bjc01/Drone_Drama_v2/D&Dv2 etch/8038 value 150dpi.png

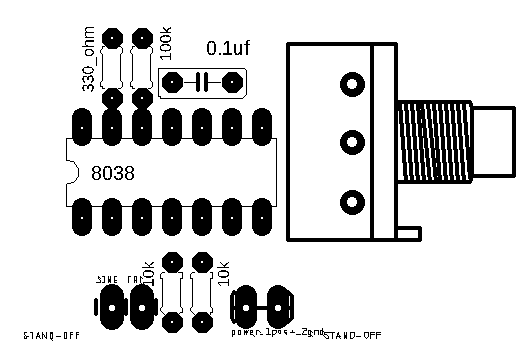
D&Dv2 etch/8038 value 150dpi.png
