bjc01/Drone_Drama_v2/D&Dv2 etch/Drama etch top 150dpi.png

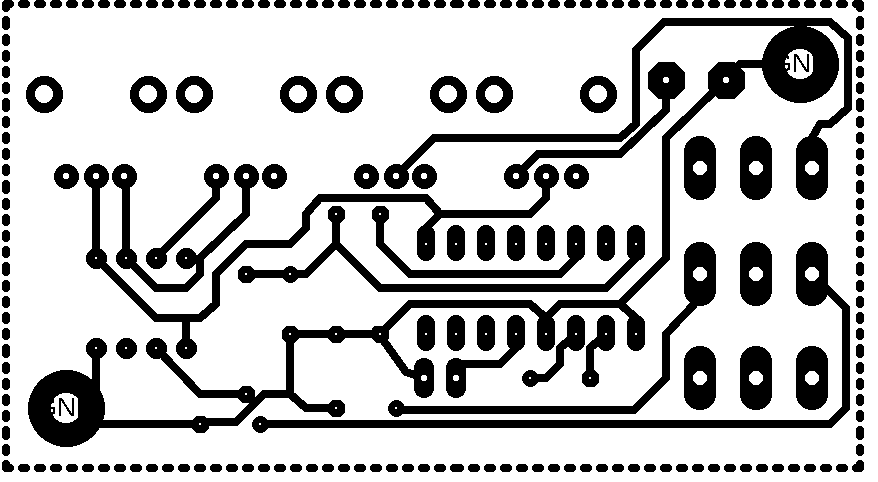
D&Dv2 etch/Drama etch top 150dpi.png
