bjc01/Drone_Drama_v2/D&Dv2 etch/filter value 150dpi.png

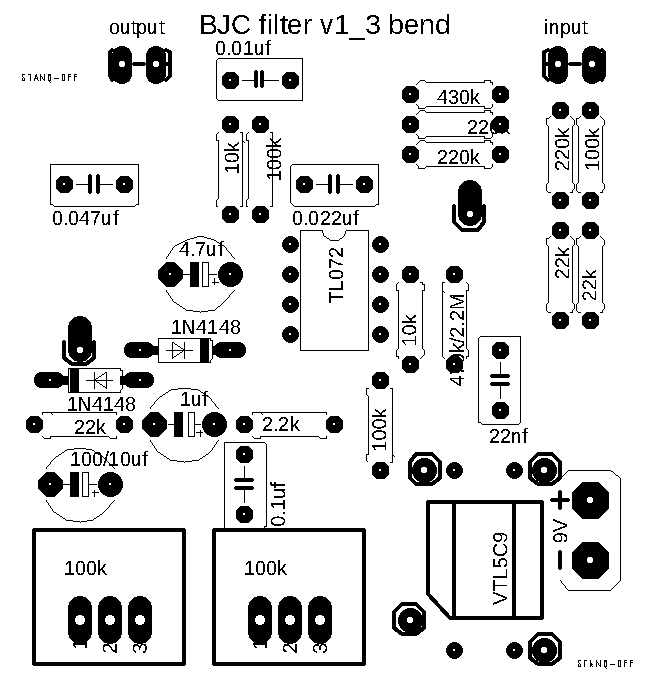
D&Dv2 etch/filter value 150dpi.png
