bjc01/Drone_Drama_v2/D&Dv2 etch/mixer etch v1 150dpi.png

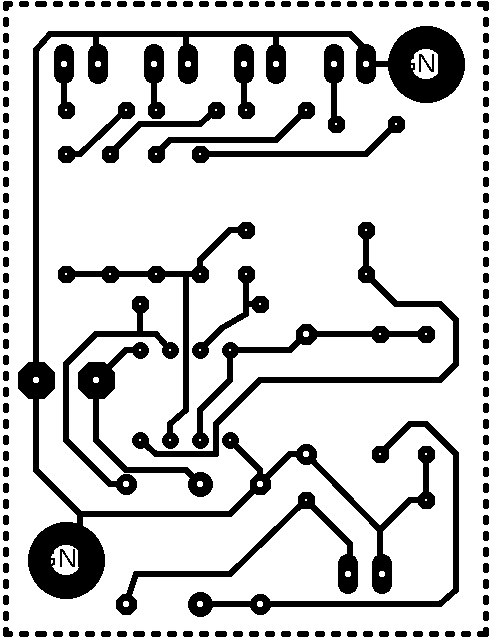
D&Dv2 etch/mixer etch v1 150dpi.png
