bjc01/Drone_Drama_v2/D&Dv2 layout/D&Dv2_filter_PCB1.png

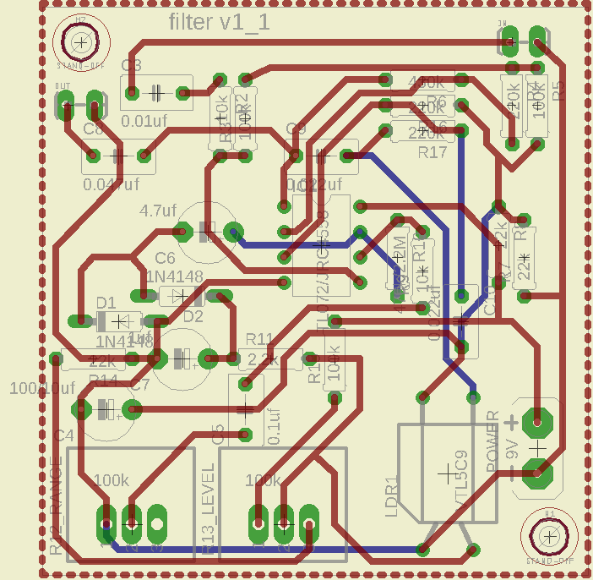
D&Dv2 layout/D&Dv2_filter_PCB1.png
